UC3Music/drawdio/media/Wiki/8.JPG

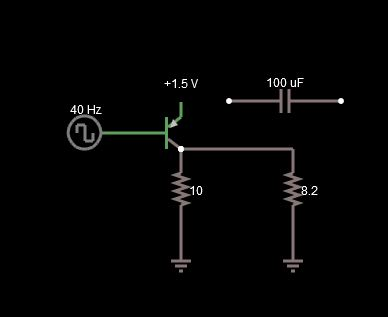
media/Wiki/8.JPG
